jdekanter077/iCEBrainstorm/documentation/stcubemx_clock_tree.png

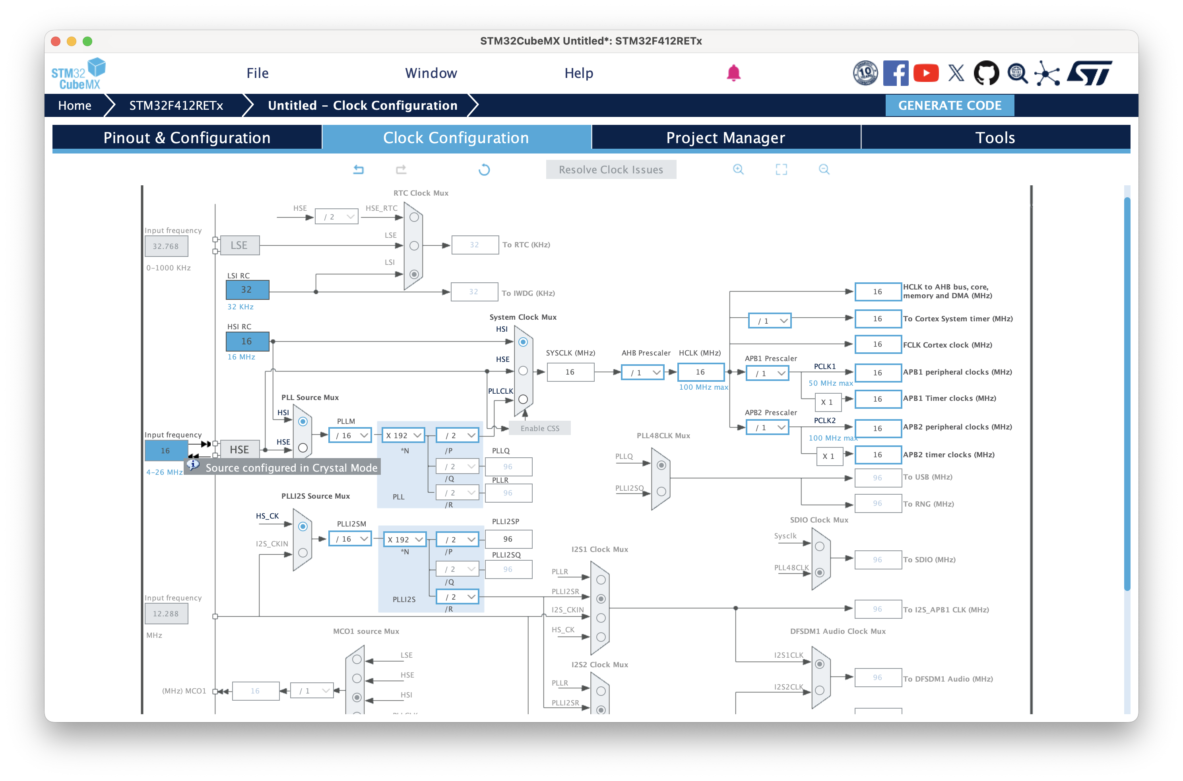
documentation/stcubemx_clock_tree.png
