jdekanter077/iCEBrainstorm/documentation/stcubemx_newproj.png

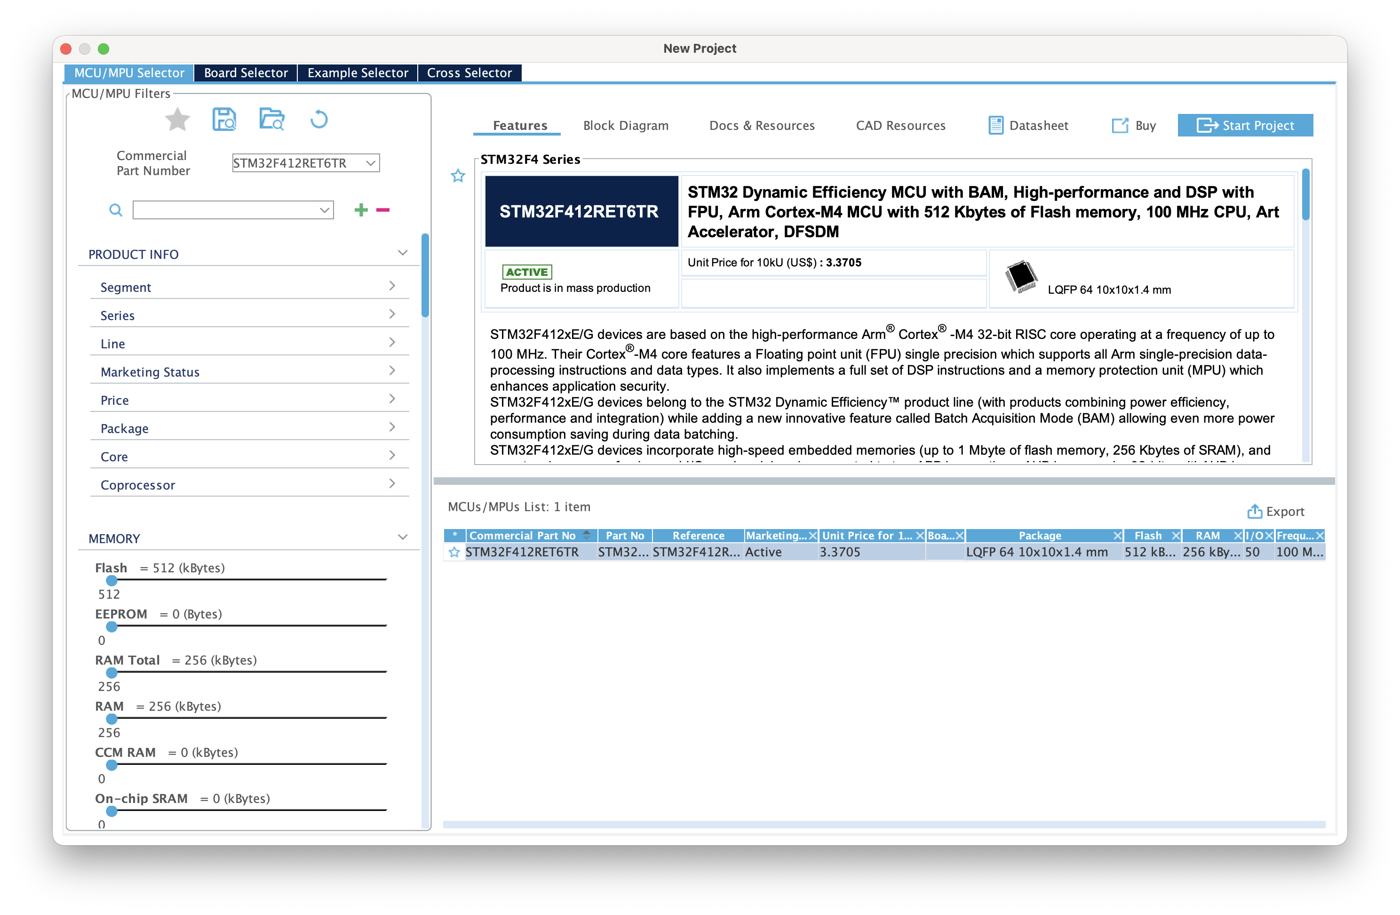
documentation/stcubemx_newproj.png
