jdekanter077/iCEBrainstorm/documentation/stcubemx_projman1.png

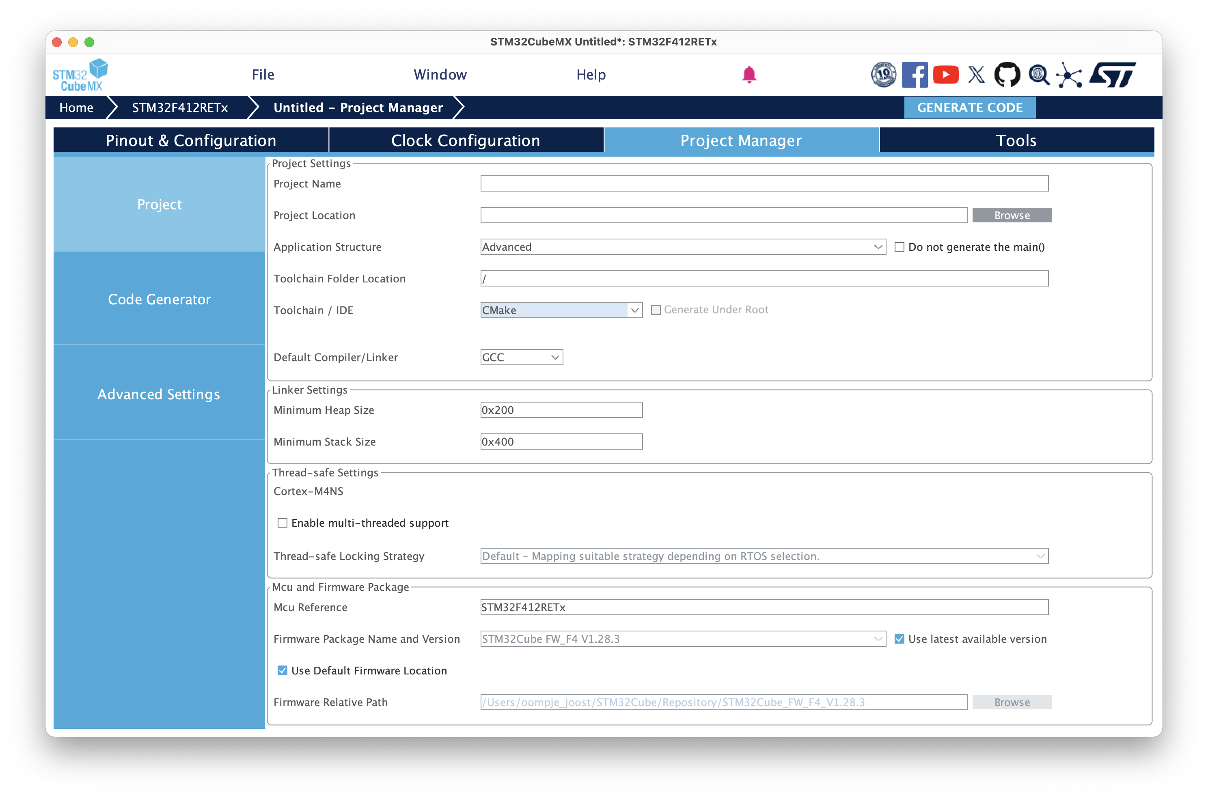
documentation/stcubemx_projman1.png
