jdekanter077/iCEBrainstorm/documentation/stcubemx_rcc_mco_2.png

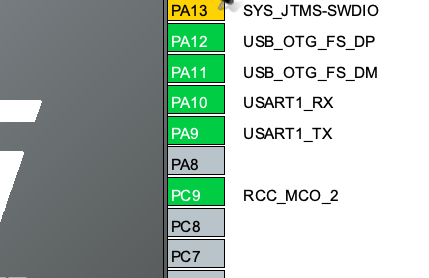
documentation/stcubemx_rcc_mco_2.png
