jdekanter077/iCEBrainstorm/documentation/vscode_compile.png

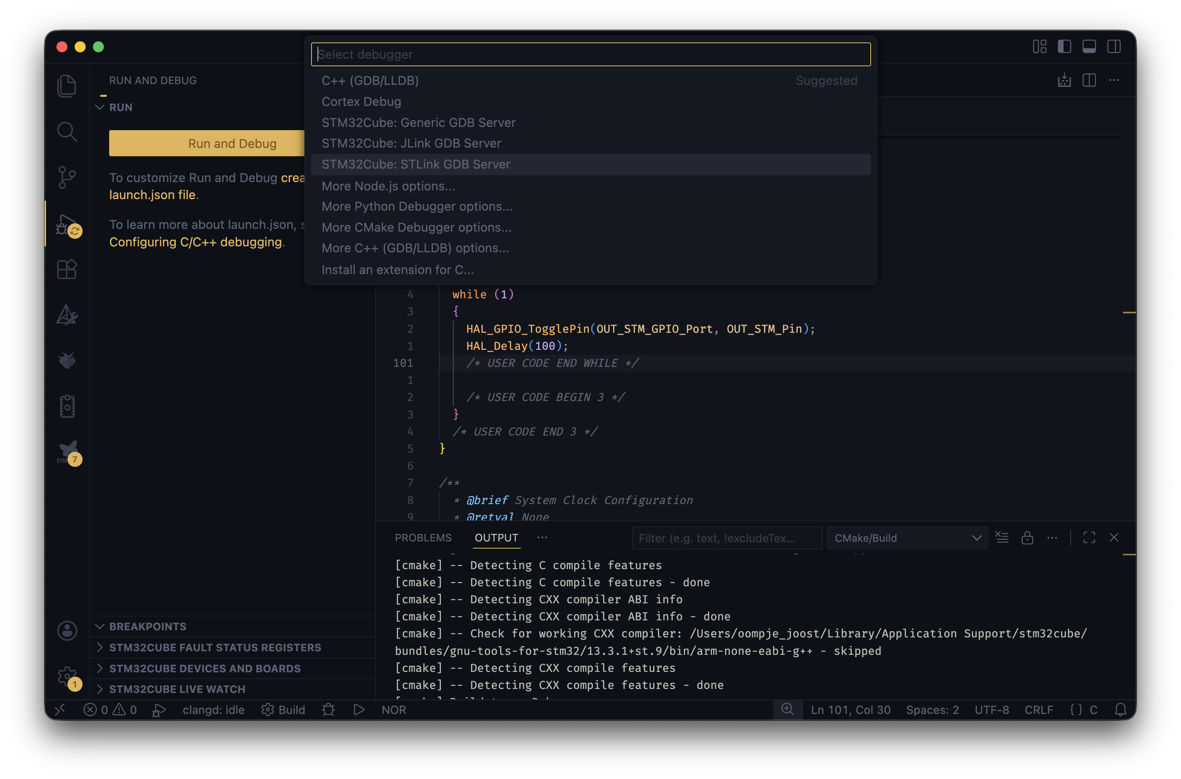
documentation/vscode_compile.png
