jdekanter077/iCEBrainstorm/documentation/Webdfu.png

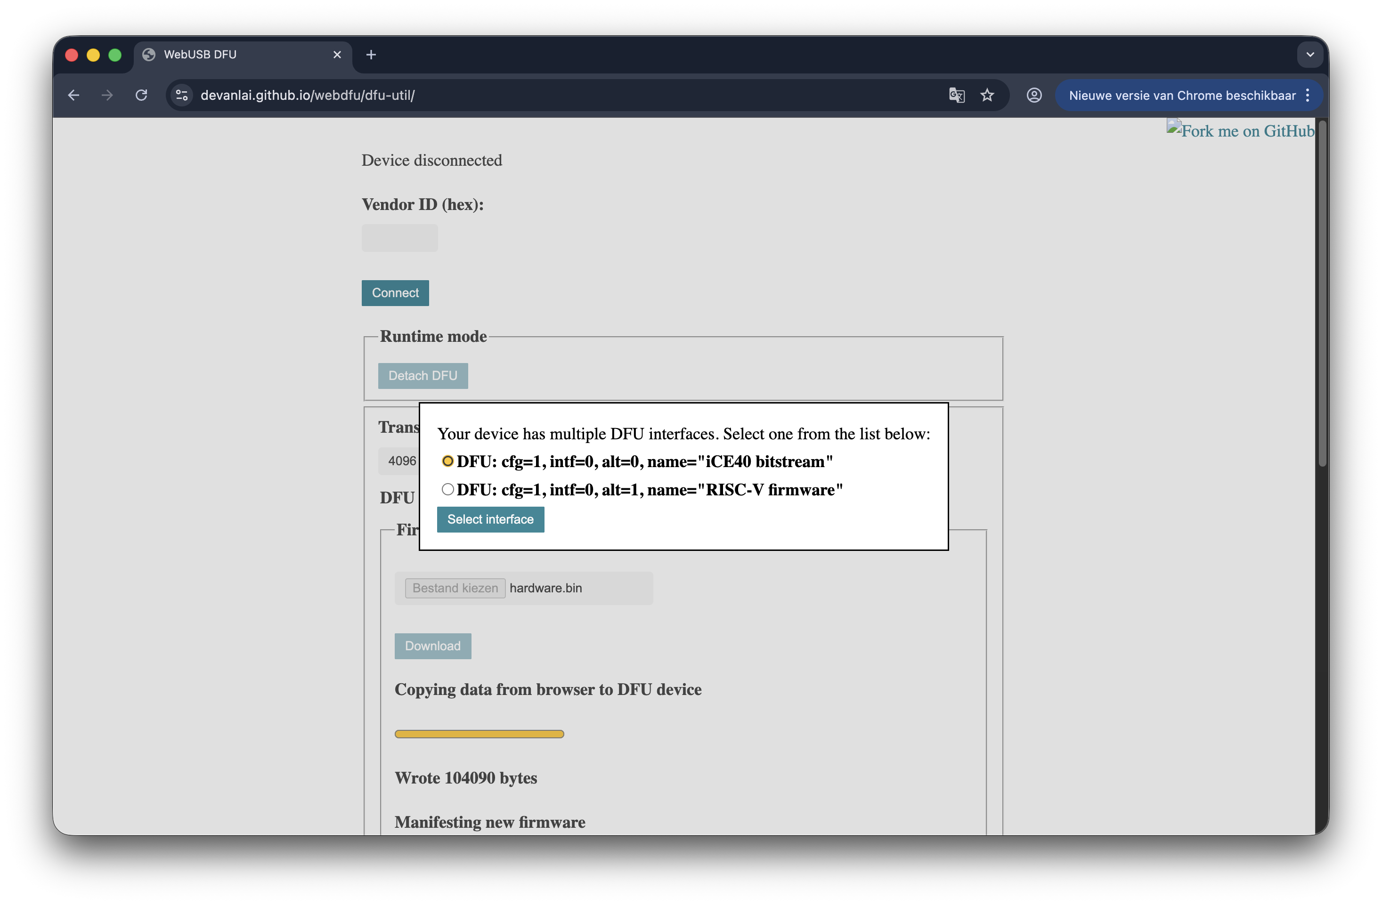
documentation/Webdfu.png
